Jost-Klancnik/Split-keyboard/Ergogen/output/outlines/standoffs_right.dxf

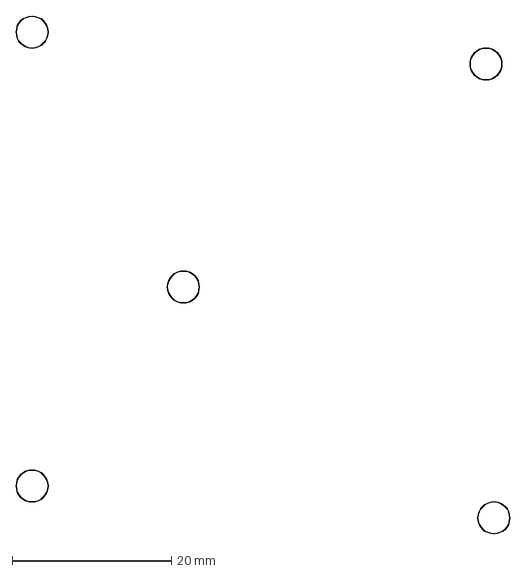
[picture p15: CAD file, 2026-02-11]
Ergogen/output/outlines/standoffs_right.dxf
62.0 x 65.0 mm
