Jost-Klancnik/Split-keyboard/Ergogen/output/outlines/walls_standoffs_left.dxf

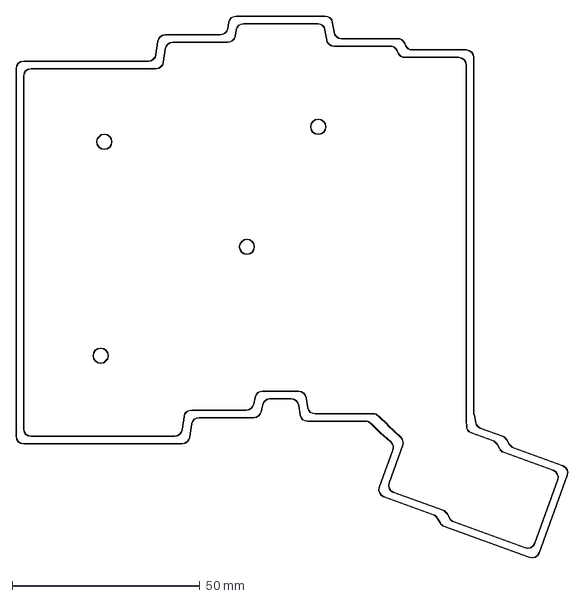
[picture p16: CAD file, 2026-02-09]
Ergogen/output/outlines/walls_standoffs_left.dxf
147.3 x 144.7 mm
