Jost-Klancnik/Split-keyboard/Ergogen/output/outlines/walls_left.dxf

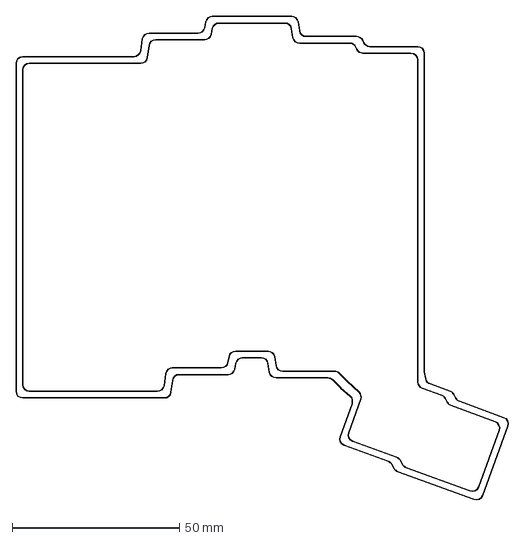
[picture p17: CAD file, 2026-02-09]
Ergogen/output/outlines/walls_left.dxf
147.3 x 144.7 mm
