Jost-Klancnik/Split-keyboard/Ergogen/output/outlines/board_left_xl.dxf

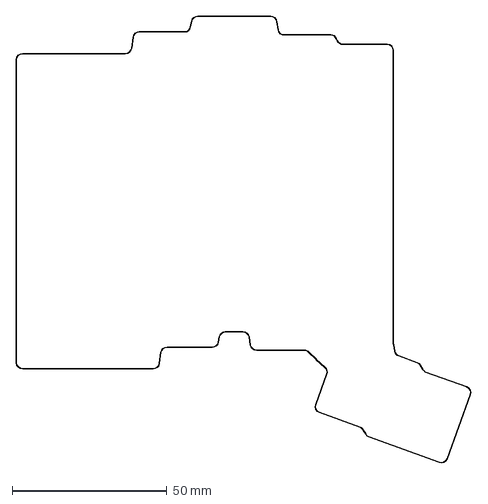
[picture p18: CAD file, 2026-02-09]
Ergogen/output/outlines/board_left_xl.dxf
147.3 x 144.7 mm
