Jost-Klancnik/Split-keyboard/Ergogen/output/outlines/standoffs_left_xl.dxf

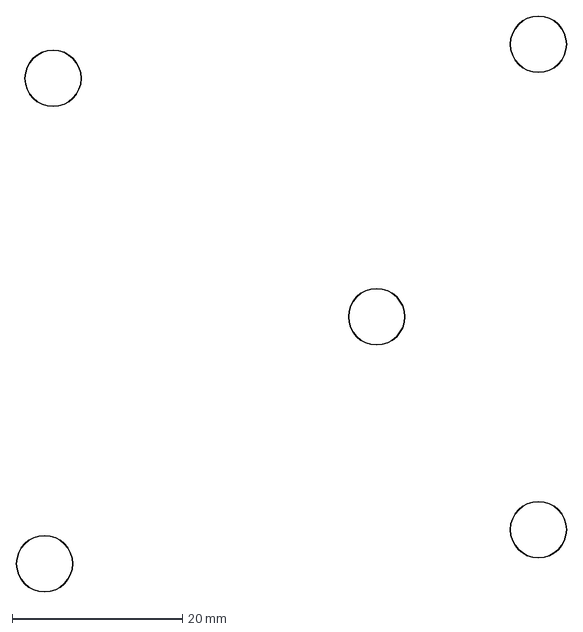
[picture p19: CAD file, 2026-02-09]
Ergogen/output/outlines/standoffs_left_xl.dxf
64.6 x 67.6 mm
