Jost-Klancnik/Split-keyboard/Ergogen/output/outlines/standoffs_left.dxf

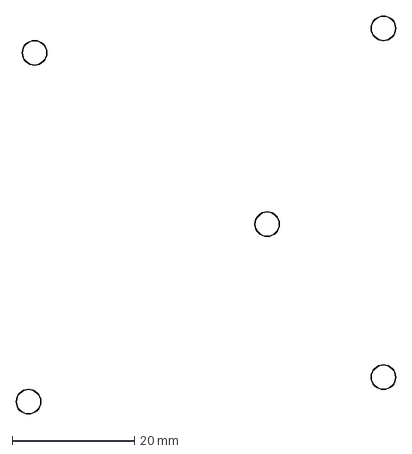
[picture p20: CAD file, 2026-02-09]
Ergogen/output/outlines/standoffs_left.dxf
62.0 x 65.0 mm
