Jost-Klancnik/Split-keyboard/Ergogen/output/outlines/standoffs_left_bottom.dxf

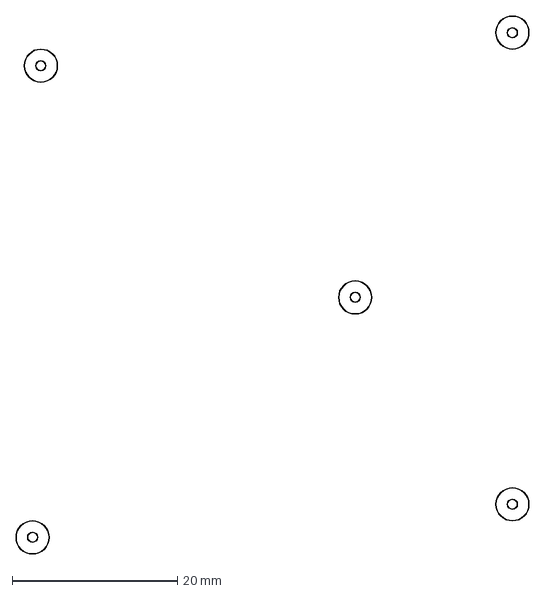
[picture p21: CAD file, 2026-02-09]
Ergogen/output/outlines/standoffs_left_bottom.dxf
62.0 x 65.0 mm
