Jost-Klancnik/Split-keyboard/Ergogen/output/outlines/standoffs_left_m.dxf

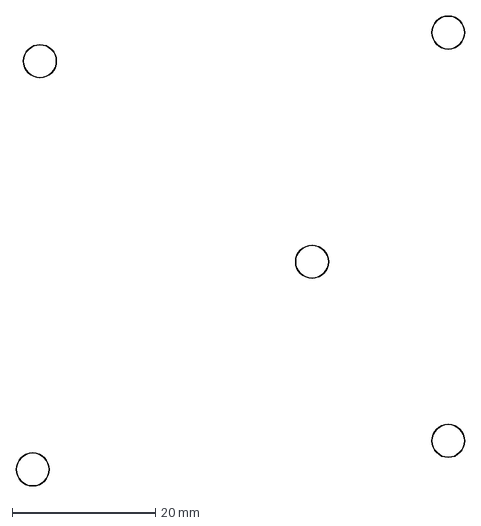
[picture p22: CAD file, 2026-02-09]
Ergogen/output/outlines/standoffs_left_m.dxf
62.6 x 65.6 mm
