Jost-Klancnik/Split-keyboard/Ergogen/output/outlines/board_left_l.dxf

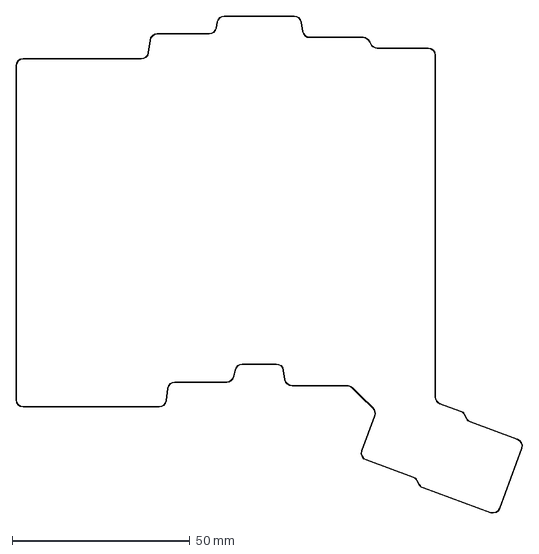
[picture p23: CAD file, 2026-02-09]
Ergogen/output/outlines/board_left_l.dxf
142.7 x 140.1 mm
