Jost-Klancnik/Split-keyboard/Ergogen/output/outlines/standoffs_thumb_left.dxf

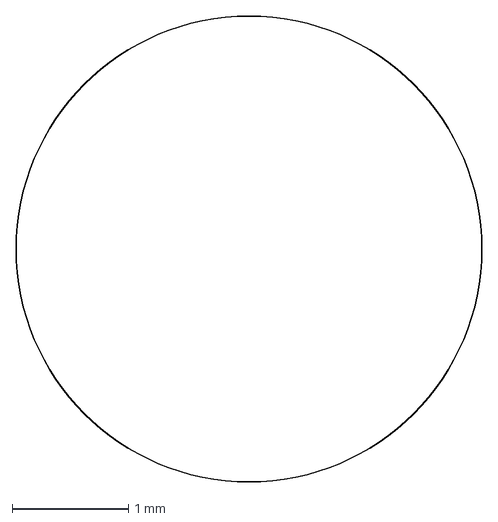
[picture p24: CAD file, 2026-02-09]
Ergogen/output/outlines/standoffs_thumb_left.dxf
4.00 x 4.00 mm
