Jost-Klancnik/Split-keyboard/Ergogen/output/outlines/standoffs_left_bottom_thumbs.dxf

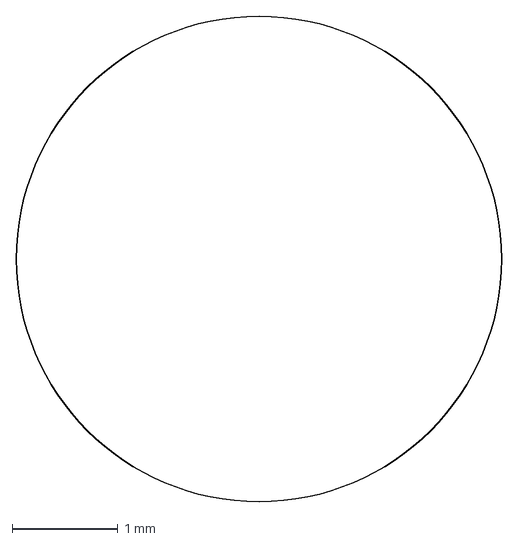
[picture p25: CAD file, 2026-02-09]
Ergogen/output/outlines/standoffs_left_bottom_thumbs.dxf
4.60 x 4.60 mm
