Jost-Klancnik/Split-keyboard/Ergogen/output/outlines/standoffs_bottom_left.dxf

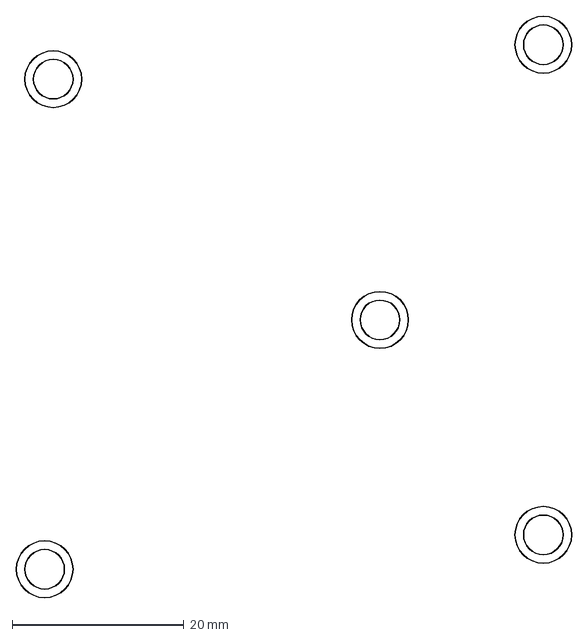
[picture p26: CAD file, 2026-02-09]
Ergogen/output/outlines/standoffs_bottom_left.dxf
64.6 x 67.6 mm
