Jost-Klancnik/Split-keyboard/Ergogen/output/outlines/board_left.dxf

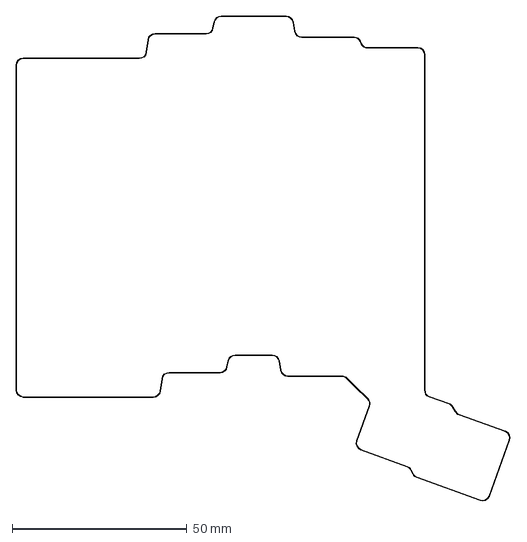
[picture p27: CAD file, 2025-10-26]
Ergogen/output/outlines/board_left.dxf
141.6 x 139.0 mm
