Jost-Klancnik/Split-keyboard/Ergogen/output/outlines/board_right.dxf

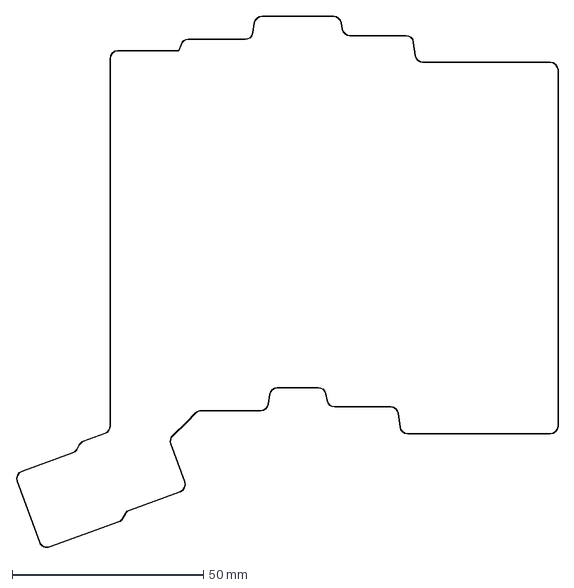
[picture p28: CAD file, 2025-10-26]
Ergogen/output/outlines/board_right.dxf
141.6 x 138.8 mm
